Danorexic/Arduino-ESP8266-RGB-Web-Server/Photos/Completed.jpg

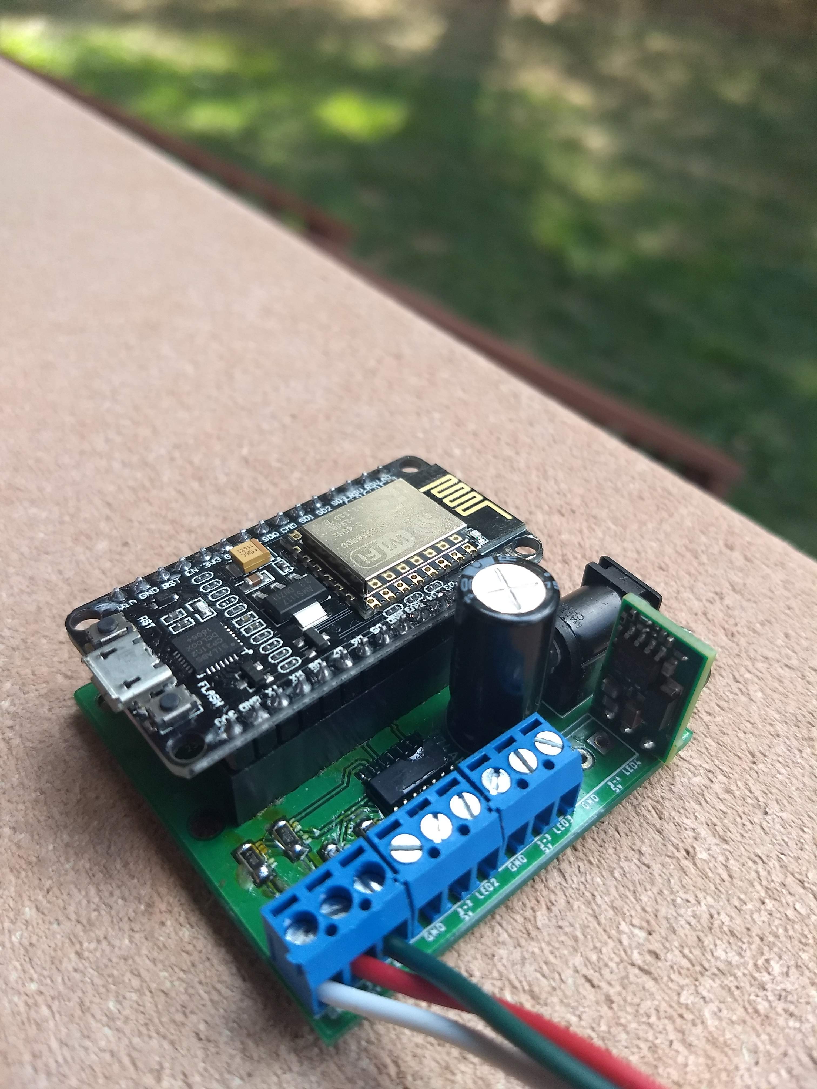
Photos/Completed.jpg
