Danorexic/Arduino-ESP8266-RGB-Web-Server/Photos/IFTTT-Brightness.JPG

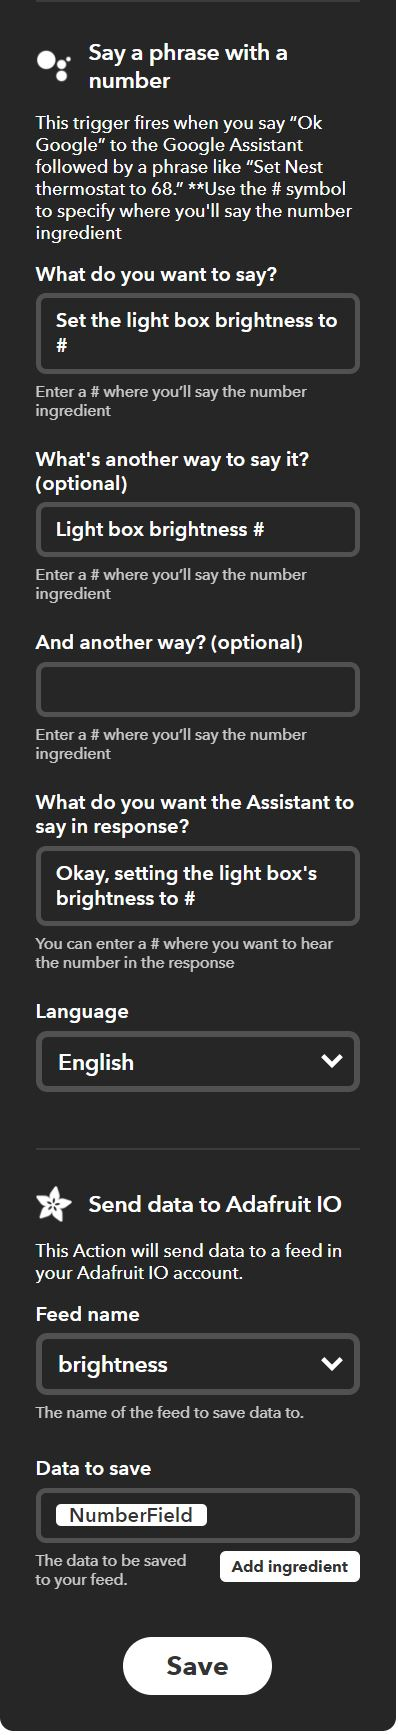
Photos/IFTTT-Brightness.JPG
