Danorexic/Arduino-ESP8266-RGB-Web-Server/Photos/IFTTT-On.JPG

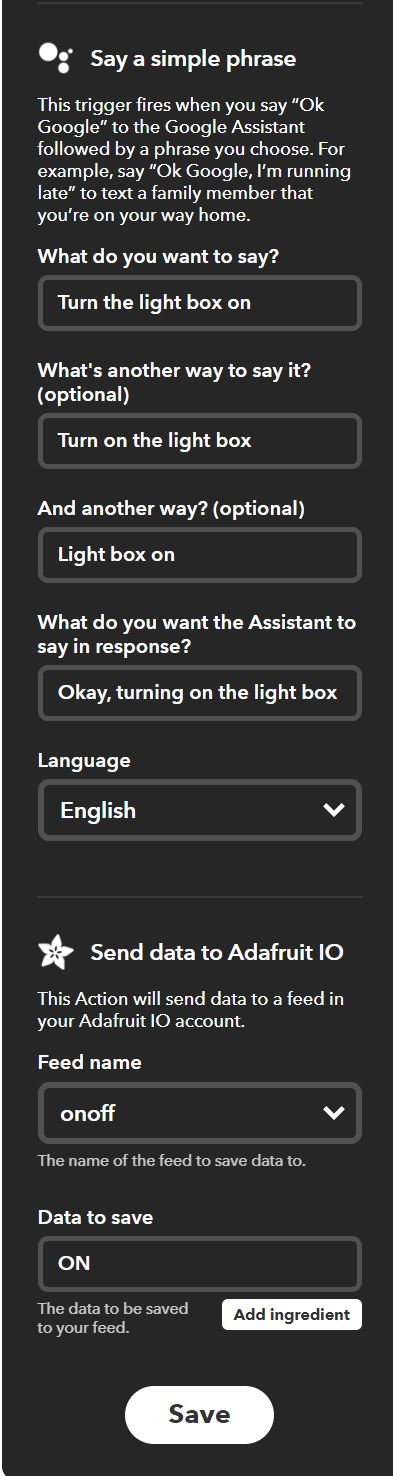
Photos/IFTTT-On.JPG
